connorl309/Z80-Drop-In/z80_rtl/z80_rtl.srcs/sources_1/new/data_bus_gater.v

`timescale 1ns / 1ps
//////////////////////////////////////////////////////////////////////////////////
// Company: 
// Engineer: 
// 
// Create Date: 02/15/2025 08:56:08 PM
// Design Name: 
// Module Name: data_bus_gater
// Project Name: 
// Target Devices: 
// Tool Versions: 
// Description: 
// 
// Dependencies: 
// 
// Revision:
// Revision 0.01 - File Created
// Additional Comments:
// 
//////////////////////////////////////////////////////////////////////////////////


module data_bus_gater(
    output [7:0] D_OUT,
    input [7:0] MDRL,
    input GATE_MDRL,
    input [7:0] MDRH,
    input GATE_MDRH
    );
endmodule
