connorl309/Z80-Drop-In/z80_rtl/z80_rtl.srcs/sources_1/bd/bd_tb_uart/ip/bd_tb_uart_fifo_generator_0_0/bd_tb_uart_fifo_generator_0_0_sim_netlist.v

// Copyright 1986-2022 Xilinx, Inc. All Rights Reserved.
// Copyright 2022-2024 Advanced Micro Devices, Inc. All Rights Reserved.
// --------------------------------------------------------------------------------
// Tool Version: Vivado v.2024.1 (win64) Build 5076996 Wed May 22 18:37:14 MDT 2024
// Date        : Sat Jan 25 12:34:48 2025
// Host        : UwU running 64-bit major release  (build 9200)
// Command     : write_verilog -force -mode funcsim -rename_top bd_tb_uart_fifo_generator_0_0 -prefix
//               bd_tb_uart_fifo_generator_0_0_ USB_Serial_Test_fifo_generator_1_0_sim_netlist.v
// Design      : USB_Serial_Test_fifo_generator_1_0
// Purpose     : This verilog netlist is a functional simulation representation of the design and should not be modified
//               or synthesized. This netlist cannot be used for SDF annotated simulation.
// Device      : xc7s50csga324-1
// --------------------------------------------------------------------------------
`timescale 1 ps / 1 ps

(* CHECK_LICENSE_TYPE = "USB_Serial_Test_fifo_generator_1_0,fifo_generator_v13_2_10,{}" *) (* downgradeipidentifiedwarnings = "yes" *) (* x_core_info = "fifo_generator_v13_2_10,Vivado 2024.1" *) 
(* NotValidForBitStream *)
module bd_tb_uart_fifo_generator_0_0
   (clk,
    rst,
    din,
    wr_en,
    rd_en,
    dout,
    full,
    empty);
  (* x_interface_info = "xilinx.com:signal:clock:1.0 core_clk CLK" *) (* x_interface_parameter = "XIL_INTERFACENAME core_clk, FREQ_HZ 100000000, FREQ_TOLERANCE_HZ 0, PHASE 0.0, CLK_DOMAIN /clk_wiz_0_clk_out1, INSERT_VIP 0" *) input clk;
  input rst;
  (* x_interface_info = "xilinx.com:interface:fifo_write:1.0 FIFO_WRITE WR_DATA" *) input [7:0]din;
  (* x_interface_info = "xilinx.com:interface:fifo_write:1.0 FIFO_WRITE WR_EN" *) input wr_en;
  (* x_interface_info = "xilinx.com:interface:fifo_read:1.0 FIFO_READ RD_EN" *) input rd_en;
  (* x_interface_info = "xilinx.com:interface:fifo_read:1.0 FIFO_READ RD_DATA" *) output [7:0]dout;
  (* x_interface_info = "xilinx.com:interface:fifo_write:1.0 FIFO_WRITE FULL" *) output full;
  (* x_interface_info = "xilinx.com:interface:fifo_read:1.0 FIFO_READ EMPTY" *) output empty;

  wire clk;
  wire [7:0]din;
  wire [7:0]dout;
  wire empty;
  wire full;
  wire rd_en;
  wire rst;
  wire wr_en;
  wire NLW_U0_almost_empty_UNCONNECTED;
  wire NLW_U0_almost_full_UNCONNECTED;
  wire NLW_U0_axi_ar_dbiterr_UNCONNECTED;
  wire NLW_U0_axi_ar_overflow_UNCONNECTED;
  wire NLW_U0_axi_ar_prog_empty_UNCONNECTED;
  wire NLW_U0_axi_ar_prog_full_UNCONNECTED;
  wire NLW_U0_axi_ar_sbiterr_UNCONNECTED;
  wire NLW_U0_axi_ar_underflow_UNCONNECTED;
  wire NLW_U0_axi_aw_dbiterr_UNCONNECTED;
  wire NLW_U0_axi_aw_overflow_UNCONNECTED;
  wire NLW_U0_axi_aw_prog_empty_UNCONNECTED;
  wire NLW_U0_axi_aw_prog_full_UNCONNECTED;
  wire NLW_U0_axi_aw_sbiterr_UNCONNECTED;
  wire NLW_U0_axi_aw_underflow_UNCONNECTED;
  wire NLW_U0_axi_b_dbiterr_UNCONNECTED;
  wire NLW_U0_axi_b_overflow_UNCONNECTED;
  wire NLW_U0_axi_b_prog_empty_UNCONNECTED;
  wire NLW_U0_axi_b_prog_full_UNCONNECTED;
  wire NLW_U0_axi_b_sbiterr_UNCONNECTED;
  wire NLW_U0_axi_b_underflow_UNCONNECTED;
  wire NLW_U0_axi_r_dbiterr_UNCONNECTED;
  wire NLW_U0_axi_r_overflow_UNCONNECTED;
  wire NLW_U0_axi_r_prog_empty_UNCONNECTED;
  wire NLW_U0_axi_r_prog_full_UNCONNECTED;
  wire NLW_U0_axi_r_sbiterr_UNCONNECTED;
  wire NLW_U0_axi_r_underflow_UNCONNECTED;
  wire NLW_U0_axi_w_dbiterr_UNCONNECTED;
  wire NLW_U0_axi_w_overflow_UNCONNECTED;
  wire NLW_U0_axi_w_prog_empty_UNCONNECTED;
  wire NLW_U0_axi_w_prog_full_UNCONNECTED;
  wire NLW_U0_axi_w_sbiterr_UNCONNECTED;
  wire NLW_U0_axi_w_underflow_UNCONNECTED;
  wire NLW_U0_axis_dbiterr_UNCONNECTED;
  wire NLW_U0_axis_overflow_UNCONNECTED;
  wire NLW_U0_axis_prog_empty_UNCONNECTED;
  wire NLW_U0_axis_prog_full_UNCONNECTED;
  wire NLW_U0_axis_sbiterr_UNCONNECTED;
  wire NLW_U0_axis_underflow_UNCONNECTED;
  wire NLW_U0_dbiterr_UNCONNECTED;
  wire NLW_U0_m_axi_arvalid_UNCONNECTED;
  wire NLW_U0_m_axi_awvalid_UNCONNECTED;
  wire NLW_U0_m_axi_bready_UNCONNECTED;
  wire NLW_U0_m_axi_rready_UNCONNECTED;
  wire NLW_U0_m_axi_wlast_UNCONNECTED;
  wire NLW_U0_m_axi_wvalid_UNCONNECTED;
  wire NLW_U0_m_axis_tlast_UNCONNECTED;
  wire NLW_U0_m_axis_tvalid_UNCONNECTED;
  wire NLW_U0_overflow_UNCONNECTED;
  wire NLW_U0_prog_empty_UNCONNECTED;
  wire NLW_U0_prog_full_UNCONNECTED;
  wire NLW_U0_rd_rst_busy_UNCONNECTED;
  wire NLW_U0_s_axi_arready_UNCONNECTED;
  wire NLW_U0_s_axi_awready_UNCONNECTED;
  wire NLW_U0_s_axi_bvalid_UNCONNECTED;
  wire NLW_U0_s_axi_rlast_UNCONNECTED;
  wire NLW_U0_s_axi_rvalid_UNCONNECTED;
  wire NLW_U0_s_axi_wready_UNCONNECTED;
  wire NLW_U0_s_axis_tready_UNCONNECTED;
  wire NLW_U0_sbiterr_UNCONNECTED;
  wire NLW_U0_underflow_UNCONNECTED;
  wire NLW_U0_valid_UNCONNECTED;
  wire NLW_U0_wr_ack_UNCONNECTED;
  wire NLW_U0_wr_rst_busy_UNCONNECTED;
  wire [4:0]NLW_U0_axi_ar_data_count_UNCONNECTED;
  wire [4:0]NLW_U0_axi_ar_rd_data_count_UNCONNECTED;
  wire [4:0]NLW_U0_axi_ar_wr_data_count_UNCONNECTED;
  wire [4:0]NLW_U0_axi_aw_data_count_UNCONNECTED;
  wire [4:0]NLW_U0_axi_aw_rd_data_count_UNCONNECTED;
  wire [4:0]NLW_U0_axi_aw_wr_data_count_UNCONNECTED;
  wire [4:0]NLW_U0_axi_b_data_count_UNCONNECTED;
  wire [4:0]NLW_U0_axi_b_rd_data_count_UNCONNECTED;
  wire [4:0]NLW_U0_axi_b_wr_data_count_UNCONNECTED;
  wire [10:0]NLW_U0_axi_r_data_count_UNCONNECTED;
  wire [10:0]NLW_U0_axi_r_rd_data_count_UNCONNECTED;
  wire [10:0]NLW_U0_axi_r_wr_data_count_UNCONNECTED;
  wire [10:0]NLW_U0_axi_w_data_count_UNCONNECTED;
  wire [10:0]NLW_U0_axi_w_rd_data_count_UNCONNECTED;
  wire [10:0]NLW_U0_axi_w_wr_data_count_UNCONNECTED;
  wire [10:0]NLW_U0_axis_data_count_UNCONNECTED;
  wire [10:0]NLW_U0_axis_rd_data_count_UNCONNECTED;
  wire [10:0]NLW_U0_axis_wr_data_count_UNCONNECTED;
  wire [9:0]NLW_U0_data_count_UNCONNECTED;
  wire [31:0]NLW_U0_m_axi_araddr_UNCONNECTED;
  wire [1:0]NLW_U0_m_axi_arburst_UNCONNECTED;
  wire [3:0]NLW_U0_m_axi_arcache_UNCONNECTED;
  wire [0:0]NLW_U0_m_axi_arid_UNCONNECTED;
  wire [7:0]NLW_U0_m_axi_arlen_UNCONNECTED;
  wire [0:0]NLW_U0_m_axi_arlock_UNCONNECTED;
  wire [2:0]NLW_U0_m_axi_arprot_UNCONNECTED;
  wire [3:0]NLW_U0_m_axi_arqos_UNCONNECTED;
  wire [3:0]NLW_U0_m_axi_arregion_UNCONNECTED;
  wire [2:0]NLW_U0_m_axi_arsize_UNCONNECTED;
  wire [0:0]NLW_U0_m_axi_aruser_UNCONNECTED;
  wire [31:0]NLW_U0_m_axi_awaddr_UNCONNECTED;
  wire [1:0]NLW_U0_m_axi_awburst_UNCONNECTED;
  wire [3:0]NLW_U0_m_axi_awcache_UNCONNECTED;
  wire [0:0]NLW_U0_m_axi_awid_UNCONNECTED;
  wire [7:0]NLW_U0_m_axi_awlen_UNCONNECTED;
  wire [0:0]NLW_U0_m_axi_awlock_UNCONNECTED;
  wire [2:0]NLW_U0_m_axi_awprot_UNCONNECTED;
  wire [3:0]NLW_U0_m_axi_awqos_UNCONNECTED;
  wire [3:0]NLW_U0_m_axi_awregion_UNCONNECTED;
  wire [2:0]NLW_U0_m_axi_awsize_UNCONNECTED;
  wire [0:0]NLW_U0_m_axi_awuser_UNCONNECTED;
  wire [63:0]NLW_U0_m_axi_wdata_UNCONNECTED;
  wire [0:0]NLW_U0_m_axi_wid_UNCONNECTED;
  wire [7:0]NLW_U0_m_axi_wstrb_UNCONNECTED;
  wire [0:0]NLW_U0_m_axi_wuser_UNCONNECTED;
  wire [7:0]NLW_U0_m_axis_tdata_UNCONNECTED;
  wire [0:0]NLW_U0_m_axis_tdest_UNCONNECTED;
  wire [0:0]NLW_U0_m_axis_tid_UNCONNECTED;
  wire [0:0]NLW_U0_m_axis_tkeep_UNCONNECTED;
  wire [0:0]NLW_U0_m_axis_tstrb_UNCONNECTED;
  wire [3:0]NLW_U0_m_axis_tuser_UNCONNECTED;
  wire [9:0]NLW_U0_rd_data_count_UNCONNECTED;
  wire [0:0]NLW_U0_s_axi_bid_UNCONNECTED;
  wire [1:0]NLW_U0_s_axi_bresp_UNCONNECTED;
  wire [0:0]NLW_U0_s_axi_buser_UNCONNECTED;
  wire [63:0]NLW_U0_s_axi_rdata_UNCONNECTED;
  wire [0:0]NLW_U0_s_axi_rid_UNCONNECTED;
  wire [1:0]NLW_U0_s_axi_rresp_UNCONNECTED;
  wire [0:0]NLW_U0_s_axi_ruser_UNCONNECTED;
  wire [9:0]NLW_U0_wr_data_count_UNCONNECTED;

  (* C_ADD_NGC_CONSTRAINT = "0" *) 
  (* C_APPLICATION_TYPE_AXIS = "0" *) 
  (* C_APPLICATION_TYPE_RACH = "0" *) 
  (* C_APPLICATION_TYPE_RDCH = "0" *) 
  (* C_APPLICATION_TYPE_WACH = "0" *) 
  (* C_APPLICATION_TYPE_WDCH = "0" *) 
  (* C_APPLICATION_TYPE_WRCH = "0" *) 
  (* C_AXIS_TDATA_WIDTH = "8" *) 
  (* C_AXIS_TDEST_WIDTH = "1" *) 
  (* C_AXIS_TID_WIDTH = "1" *) 
  (* C_AXIS_TKEEP_WIDTH = "1" *) 
  (* C_AXIS_TSTRB_WIDTH = "1" *) 
  (* C_AXIS_TUSER_WIDTH = "4" *) 
  (* C_AXIS_TYPE = "0" *) 
  (* C_AXI_ADDR_WIDTH = "32" *) 
  (* C_AXI_ARUSER_WIDTH = "1" *) 
  (* C_AXI_AWUSER_WIDTH = "1" *) 
  (* C_AXI_BUSER_WIDTH = "1" *) 
  (* C_AXI_DATA_WIDTH = "64" *) 
  (* C_AXI_ID_WIDTH = "1" *) 
  (* C_AXI_LEN_WIDTH = "8" *) 
  (* C_AXI_LOCK_WIDTH = "1" *) 
  (* C_AXI_RUSER_WIDTH = "1" *) 
  (* C_AXI_TYPE = "1" *) 
  (* C_AXI_WUSER_WIDTH = "1" *) 
  (* C_COMMON_CLOCK = "1" *) 
  (* C_COUNT_TYPE = "0" *) 
  (* C_DATA_COUNT_WIDTH = "10" *) 
  (* C_DEFAULT_VALUE = "BlankString" *) 
  (* C_DIN_WIDTH = "8" *) 
  (* C_DIN_WIDTH_AXIS = "1" *) 
  (* C_DIN_WIDTH_RACH = "32" *) 
  (* C_DIN_WIDTH_RDCH = "64" *) 
  (* C_DIN_WIDTH_WACH = "1" *) 
  (* C_DIN_WIDTH_WDCH = "64" *) 
  (* C_DIN_WIDTH_WRCH = "2" *) 
  (* C_DOUT_RST_VAL = "0" *) 
  (* C_DOUT_WIDTH = "8" *) 
  (* C_ENABLE_RLOCS = "0" *) 
  (* C_ENABLE_RST_SYNC = "1" *) 
  (* C_EN_SAFETY_CKT = "0" *) 
  (* C_ERROR_INJECTION_TYPE = "0" *) 
  (* C_ERROR_INJECTION_TYPE_AXIS = "0" *) 
  (* C_ERROR_INJECTION_TYPE_RACH = "0" *) 
  (* C_ERROR_INJECTION_TYPE_RDCH = "0" *) 
  (* C_ERROR_INJECTION_TYPE_WACH = "0" *) 
  (* C_ERROR_INJECTION_TYPE_WDCH = "0" *) 
  (* C_ERROR_INJECTION_TYPE_WRCH = "0" *) 
  (* C_FAMILY = "spartan7" *) 
  (* C_FULL_FLAGS_RST_VAL = "0" *) 
  (* C_HAS_ALMOST_EMPTY = "0" *) 
  (* C_HAS_ALMOST_FULL = "0" *) 
  (* C_HAS_AXIS_TDATA = "1" *) 
  (* C_HAS_AXIS_TDEST = "0" *) 
  (* C_HAS_AXIS_TID = "0" *) 
  (* C_HAS_AXIS_TKEEP = "0" *) 
  (* C_HAS_AXIS_TLAST = "0" *) 
  (* C_HAS_AXIS_TREADY = "1" *) 
  (* C_HAS_AXIS_TSTRB = "0" *) 
  (* C_HAS_AXIS_TUSER = "1" *) 
  (* C_HAS_AXI_ARUSER = "0" *) 
  (* C_HAS_AXI_AWUSER = "0" *) 
  (* C_HAS_AXI_BUSER = "0" *) 
  (* C_HAS_AXI_ID = "0" *) 
  (* C_HAS_AXI_RD_CHANNEL = "1" *) 
  (* C_HAS_AXI_RUSER = "0" *) 
  (* C_HAS_AXI_WR_CHANNEL = "1" *) 
  (* C_HAS_AXI_WUSER = "0" *) 
  (* C_HAS_BACKUP = "0" *) 
  (* C_HAS_DATA_COUNT = "0" *) 
  (* C_HAS_DATA_COUNTS_AXIS = "0" *) 
  (* C_HAS_DATA_COUNTS_RACH = "0" *) 
  (* C_HAS_DATA_COUNTS_RDCH = "0" *) 
  (* C_HAS_DATA_COUNTS_WACH = "0" *) 
  (* C_HAS_DATA_COUNTS_WDCH = "0" *) 
  (* C_HAS_DATA_COUNTS_WRCH = "0" *) 
  (* C_HAS_INT_CLK = "0" *) 
  (* C_HAS_MASTER_CE = "0" *) 
  (* C_HAS_MEMINIT_FILE = "0" *) 
  (* C_HAS_OVERFLOW = "0" *) 
  (* C_HAS_PROG_FLAGS_AXIS = "0" *) 
  (* C_HAS_PROG_FLAGS_RACH = "0" *) 
  (* C_HAS_PROG_FLAGS_RDCH = "0" *) 
  (* C_HAS_PROG_FLAGS_WACH = "0" *) 
  (* C_HAS_PROG_FLAGS_WDCH = "0" *) 
  (* C_HAS_PROG_FLAGS_WRCH = "0" *) 
  (* C_HAS_RD_DATA_COUNT = "0" *) 
  (* C_HAS_RD_RST = "0" *) 
  (* C_HAS_RST = "1" *) 
  (* C_HAS_SLAVE_CE = "0" *) 
  (* C_HAS_SRST = "0" *) 
  (* C_HAS_UNDERFLOW = "0" *) 
  (* C_HAS_VALID = "0" *) 
  (* C_HAS_WR_ACK = "0" *) 
  (* C_HAS_WR_DATA_COUNT = "0" *) 
  (* C_HAS_WR_RST = "0" *) 
  (* C_IMPLEMENTATION_TYPE = "6" *) 
  (* C_IMPLEMENTATION_TYPE_AXIS = "1" *) 
  (* C_IMPLEMENTATION_TYPE_RACH = "1" *) 
  (* C_IMPLEMENTATION_TYPE_RDCH = "1" *) 
  (* C_IMPLEMENTATION_TYPE_WACH = "1" *) 
  (* C_IMPLEMENTATION_TYPE_WDCH = "1" *) 
  (* C_IMPLEMENTATION_TYPE_WRCH = "1" *) 
  (* C_INIT_WR_PNTR_VAL = "0" *) 
  (* C_INTERFACE_TYPE = "0" *) 
  (* C_MEMORY_TYPE = "4" *) 
  (* C_MIF_FILE_NAME = "BlankString" *) 
  (* C_MSGON_VAL = "1" *) 
  (* C_OPTIMIZATION_MODE = "0" *) 
  (* C_OVERFLOW_LOW = "0" *) 
  (* C_POWER_SAVING_MODE = "0" *) 
  (* C_PRELOAD_LATENCY = "1" *) 
  (* C_PRELOAD_REGS = "0" *) 
  (* C_PRIM_FIFO_TYPE = "1kx18" *) 
  (* C_PRIM_FIFO_TYPE_AXIS = "1kx18" *) 
  (* C_PRIM_FIFO_TYPE_RACH = "512x36" *) 
  (* C_PRIM_FIFO_TYPE_RDCH = "1kx36" *) 
  (* C_PRIM_FIFO_TYPE_WACH = "512x36" *) 
  (* C_PRIM_FIFO_TYPE_WDCH = "1kx36" *) 
  (* C_PRIM_FIFO_TYPE_WRCH = "512x36" *) 
  (* C_PROG_EMPTY_THRESH_ASSERT_VAL = "2" *) 
  (* C_PROG_EMPTY_THRESH_ASSERT_VAL_AXIS = "1022" *) 
  (* C_PROG_EMPTY_THRESH_ASSERT_VAL_RACH = "1022" *) 
  (* C_PROG_EMPTY_THRESH_ASSERT_VAL_RDCH = "1022" *) 
  (* C_PROG_EMPTY_THRESH_ASSERT_VAL_WACH = "1022" *) 
  (* C_PROG_EMPTY_THRESH_ASSERT_VAL_WDCH = "1022" *) 
  (* C_PROG_EMPTY_THRESH_ASSERT_VAL_WRCH = "1022" *) 
  (* C_PROG_EMPTY_THRESH_NEGATE_VAL = "3" *) 
  (* C_PROG_EMPTY_TYPE = "0" *) 
  (* C_PROG_EMPTY_TYPE_AXIS = "0" *) 
  (* C_PROG_EMPTY_TYPE_RACH = "0" *) 
  (* C_PROG_EMPTY_TYPE_RDCH = "0" *) 
  (* C_PROG_EMPTY_TYPE_WACH = "0" *) 
  (* C_PROG_EMPTY_TYPE_WDCH = "0" *) 
  (* C_PROG_EMPTY_TYPE_WRCH = "0" *) 
  (* C_PROG_FULL_THRESH_ASSERT_VAL = "1022" *) 
  (* C_PROG_FULL_THRESH_ASSERT_VAL_AXIS = "1023" *) 
  (* C_PROG_FULL_THRESH_ASSERT_VAL_RACH = "1023" *) 
  (* C_PROG_FULL_THRESH_ASSERT_VAL_RDCH = "1023" *) 
  (* C_PROG_FULL_THRESH_ASSERT_VAL_WACH = "1023" *) 
  (* C_PROG_FULL_THRESH_ASSERT_VAL_WDCH = "1023" *) 
  (* C_PROG_FULL_THRESH_ASSERT_VAL_WRCH = "1023" *) 
  (* C_PROG_FULL_THRESH_NEGATE_VAL = "1021" *) 
  (* C_PROG_FULL_TYPE = "0" *) 
  (* C_PROG_FULL_TYPE_AXIS = "0" *) 
  (* C_PROG_FULL_TYPE_RACH = "0" *) 
  (* C_PROG_FULL_TYPE_RDCH = "0" *) 
  (* C_PROG_FULL_TYPE_WACH = "0" *) 
  (* C_PROG_FULL_TYPE_WDCH = "0" *) 
  (* C_PROG_FULL_TYPE_WRCH = "0" *) 
  (* C_RACH_TYPE = "0" *) 
  (* C_RDCH_TYPE = "0" *) 
  (* C_RD_DATA_COUNT_WIDTH = "10" *) 
  (* C_RD_DEPTH = "1024" *) 
  (* C_RD_FREQ = "1" *) 
  (* C_RD_PNTR_WIDTH = "10" *) 
  (* C_REG_SLICE_MODE_AXIS = "0" *) 
  (* C_REG_SLICE_MODE_RACH = "0" *) 
  (* C_REG_SLICE_MODE_RDCH = "0" *) 
  (* C_REG_SLICE_MODE_WACH = "0" *) 
  (* C_REG_SLICE_MODE_WDCH = "0" *) 
  (* C_REG_SLICE_MODE_WRCH = "0" *) 
  (* C_SELECT_XPM = "0" *) 
  (* C_SYNCHRONIZER_STAGE = "2" *) 
  (* C_UNDERFLOW_LOW = "0" *) 
  (* C_USE_COMMON_OVERFLOW = "0" *) 
  (* C_USE_COMMON_UNDERFLOW = "0" *) 
  (* C_USE_DEFAULT_SETTINGS = "0" *) 
  (* C_USE_DOUT_RST = "0" *) 
  (* C_USE_ECC = "0" *) 
  (* C_USE_ECC_AXIS = "0" *) 
  (* C_USE_ECC_RACH = "0" *) 
  (* C_USE_ECC_RDCH = "0" *) 
  (* C_USE_ECC_WACH = "0" *) 
  (* C_USE_ECC_WDCH = "0" *) 
  (* C_USE_ECC_WRCH = "0" *) 
  (* C_USE_EMBEDDED_REG = "0" *) 
  (* C_USE_FIFO16_FLAGS = "0" *) 
  (* C_USE_FWFT_DATA_COUNT = "0" *) 
  (* C_USE_PIPELINE_REG = "0" *) 
  (* C_VALID_LOW = "0" *) 
  (* C_WACH_TYPE = "0" *) 
  (* C_WDCH_TYPE = "0" *) 
  (* C_WRCH_TYPE = "0" *) 
  (* C_WR_ACK_LOW = "0" *) 
  (* C_WR_DATA_COUNT_WIDTH = "10" *) 
  (* C_WR_DEPTH = "1024" *) 
  (* C_WR_DEPTH_AXIS = "1024" *) 
  (* C_WR_DEPTH_RACH = "16" *) 
  (* C_WR_DEPTH_RDCH = "1024" *) 
  (* C_WR_DEPTH_WACH = "16" *) 
  (* C_WR_DEPTH_WDCH = "1024" *) 
  (* C_WR_DEPTH_WRCH = "16" *) 
  (* C_WR_FREQ = "1" *) 
  (* C_WR_PNTR_WIDTH = "10" *) 
  (* C_WR_PNTR_WIDTH_AXIS = "10" *) 
  (* C_WR_PNTR_WIDTH_RACH = "4" *) 
  (* C_WR_PNTR_WIDTH_RDCH = "10" *) 
  (* C_WR_PNTR_WIDTH_WACH = "4" *) 
  (* C_WR_PNTR_WIDTH_WDCH = "10" *) 
  (* C_WR_PNTR_WIDTH_WRCH = "4" *) 
  (* C_WR_RESPONSE_LATENCY = "1" *) 
  (* is_du_within_envelope = "true" *) 
  bd_tb_uart_fifo_generator_0_0_fifo_generator_v13_2_10 U0
       (.almost_empty(NLW_U0_almost_empty_UNCONNECTED),
        .almost_full(NLW_U0_almost_full_UNCONNECTED),
        .axi_ar_data_count(NLW_U0_axi_ar_data_count_UNCONNECTED[4:0]),
        .axi_ar_dbiterr(NLW_U0_axi_ar_dbiterr_UNCONNECTED),
        .axi_ar_injectdbiterr(1'b0),
        .axi_ar_injectsbiterr(1'b0),
        .axi_ar_overflow(NLW_U0_axi_ar_overflow_UNCONNECTED),
        .axi_ar_prog_empty(NLW_U0_axi_ar_prog_empty_UNCONNECTED),
        .axi_ar_prog_empty_thresh({1'b0,1'b0,1'b0,1'b0}),
        .axi_ar_prog_full(NLW_U0_axi_ar_prog_full_UNCONNECTED),
        .axi_ar_prog_full_thresh({1'b0,1'b0,1'b0,1'b0}),
        .axi_ar_rd_data_count(NLW_U0_axi_ar_rd_data_count_UNCONNECTED[4:0]),
        .axi_ar_sbiterr(NLW_U0_axi_ar_sbiterr_UNCONNECTED),
        .axi_ar_underflow(NLW_U0_axi_ar_underflow_UNCONNECTED),
        .axi_ar_wr_data_count(NLW_U0_axi_ar_wr_data_count_UNCONNECTED[4:0]),
        .axi_aw_data_count(NLW_U0_axi_aw_data_count_UNCONNECTED[4:0]),
        .axi_aw_dbiterr(NLW_U0_axi_aw_dbiterr_UNCONNECTED),
        .axi_aw_injectdbiterr(1'b0),
        .axi_aw_injectsbiterr(1'b0),
        .axi_aw_overflow(NLW_U0_axi_aw_overflow_UNCONNECTED),
        .axi_aw_prog_empty(NLW_U0_axi_aw_prog_empty_UNCONNECTED),
        .axi_aw_prog_empty_thresh({1'b0,1'b0,1'b0,1'b0}),
        .axi_aw_prog_full(NLW_U0_axi_aw_prog_full_UNCONNECTED),
        .axi_aw_prog_full_thresh({1'b0,1'b0,1'b0,1'b0}),
        .axi_aw_rd_data_count(NLW_U0_axi_aw_rd_data_count_UNCONNECTED[4:0]),
        .axi_aw_sbiterr(NLW_U0_axi_aw_sbiterr_UNCONNECTED),
        .axi_aw_underflow(NLW_U0_axi_aw_underflow_UNCONNECTED),
        .axi_aw_wr_data_count(NLW_U0_axi_aw_wr_data_count_UNCONNECTED[4:0]),
        .axi_b_data_count(NLW_U0_axi_b_data_count_UNCONNECTED[4:0]),
        .axi_b_dbiterr(NLW_U0_axi_b_dbiterr_UNCONNECTED),
        .axi_b_injectdbiterr(1'b0),
        .axi_b_injectsbiterr(1'b0),
        .axi_b_overflow(NLW_U0_axi_b_overflow_UNCONNECTED),
        .axi_b_prog_empty(NLW_U0_axi_b_prog_empty_UNCONNECTED),
        .axi_b_prog_empty_thresh({1'b0,1'b0,1'b0,1'b0}),
        .axi_b_prog_full(NLW_U0_axi_b_prog_full_UNCONNECTED),
        .axi_b_prog_full_thresh({1'b0,1'b0,1'b0,1'b0}),
        .axi_b_rd_data_count(NLW_U0_axi_b_rd_data_count_UNCONNECTED[4:0]),
        .axi_b_sbiterr(NLW_U0_axi_b_sbiterr_UNCONNECTED),
        .axi_b_underflow(NLW_U0_axi_b_underflow_UNCONNECTED),
        .axi_b_wr_data_count(NLW_U0_axi_b_wr_data_count_UNCONNECTED[4:0]),
        .axi_r_data_count(NLW_U0_axi_r_data_count_UNCONNECTED[10:0]),
        .axi_r_dbiterr(NLW_U0_axi_r_dbiterr_UNCONNECTED),
        .axi_r_injectdbiterr(1'b0),
        .axi_r_injectsbiterr(1'b0),
        .axi_r_overflow(NLW_U0_axi_r_overflow_UNCONNECTED),
        .axi_r_prog_empty(NLW_U0_axi_r_prog_empty_UNCONNECTED),
        .axi_r_prog_empty_thresh({1'b0,1'b0,1'b0,1'b0,1'b0,1'b0,1'b0,1'b0,1'b0,1'b0}),
        .axi_r_prog_full(NLW_U0_axi_r_prog_full_UNCONNECTED),
        .axi_r_prog_full_thresh({1'b0,1'b0,1'b0,1'b0,1'b0,1'b0,1'b0,1'b0,1'b0,1'b0}),
        .axi_r_rd_data_count(NLW_U0_axi_r_rd_data_count_UNCONNECTED[10:0]),
        .axi_r_sbiterr(NLW_U0_axi_r_sbiterr_UNCONNECTED),
        .axi_r_underflow(NLW_U0_axi_r_underflow_UNCONNECTED),
        .axi_r_wr_data_count(NLW_U0_axi_r_wr_data_count_UNCONNECTED[10:0]),
        .axi_w_data_count(NLW_U0_axi_w_data_count_UNCONNECTED[10:0]),
        .axi_w_dbiterr(NLW_U0_axi_w_dbiterr_UNCONNECTED),
        .axi_w_injectdbiterr(1'b0),
        .axi_w_injectsbiterr(1'b0),
        .axi_w_overflow(NLW_U0_axi_w_overflow_UNCONNECTED),
        .axi_w_prog_empty(NLW_U0_axi_w_prog_empty_UNCONNECTED),
        .axi_w_prog_empty_thresh({1'b0,1'b0,1'b0,1'b0,1'b0,1'b0,1'b0,1'b0,1'b0,1'b0}),
        .axi_w_prog_full(NLW_U0_axi_w_prog_full_UNCONNECTED),
        .axi_w_prog_full_thresh({1'b0,1'b0,1'b0,1'b0,1'b0,1'b0,1'b0,1'b0,1'b0,1'b0}),
        .axi_w_rd_data_count(NLW_U0_axi_w_rd_data_count_UNCONNECTED[10:0]),
        .axi_w_sbiterr(NLW_U0_axi_w_sbiterr_UNCONNECTED),
        .axi_w_underflow(NLW_U0_axi_w_underflow_UNCONNECTED),
        .axi_w_wr_data_count(NLW_U0_axi_w_wr_data_count_UNCONNECTED[10:0]),
        .axis_data_count(NLW_U0_axis_data_count_UNCONNECTED[10:0]),
        .axis_dbiterr(NLW_U0_axis_dbiterr_UNCONNECTED),
        .axis_injectdbiterr(1'b0),
        .axis_injectsbiterr(1'b0),
        .axis_overflow(NLW_U0_axis_overflow_UNCONNECTED),
        .axis_prog_empty(NLW_U0_axis_prog_empty_UNCONNECTED),
        .axis_prog_empty_thresh({1'b0,1'b0,1'b0,1'b0,1'b0,1'b0,1'b0,1'b0,1'b0,1'b0}),
        .axis_prog_full(NLW_U0_axis_prog_full_UNCONNECTED),
        .axis_prog_full_thresh({1'b0,1'b0,1'b0,1'b0,1'b0,1'b0,1'b0,1'b0,1'b0,1'b0}),
        .axis_rd_data_count(NLW_U0_axis_rd_data_count_UNCONNECTED[10:0]),
        .axis_sbiterr(NLW_U0_axis_sbiterr_UNCONNECTED),
        .axis_underflow(NLW_U0_axis_underflow_UNCONNECTED),
        .axis_wr_data_count(NLW_U0_axis_wr_data_count_UNCONNECTED[10:0]),
        .backup(1'b0),
        .backup_marker(1'b0),
        .clk(clk),
        .data_count(NLW_U0_data_count_UNCONNECTED[9:0]),
        .dbiterr(NLW_U0_dbiterr_UNCONNECTED),
        .din(din),
        .dout(dout),
        .empty(empty),
        .full(full),
        .injectdbiterr(1'b0),
        .injectsbiterr(1'b0),
        .int_clk(1'b0),
        .m_aclk(1'b0),
        .m_aclk_en(1'b0),
        .m_axi_araddr(NLW_U0_m_axi_araddr_UNCONNECTED[31:0]),
        .m_axi_arburst(NLW_U0_m_axi_arburst_UNCONNECTED[1:0]),
        .m_axi_arcache(NLW_U0_m_axi_arcache_UNCONNECTED[3:0]),
        .m_axi_arid(NLW_U0_m_axi_arid_UNCONNECTED[0]),
        .m_axi_arlen(NLW_U0_m_axi_arlen_UNCONNECTED[7:0]),
        .m_axi_arlock(NLW_U0_m_axi_arlock_UNCONNECTED[0]),
        .m_axi_arprot(NLW_U0_m_axi_arprot_UNCONNECTED[2:0]),
        .m_axi_arqos(NLW_U0_m_axi_arqos_UNCONNECTED[3:0]),
        .m_axi_arready(1'b0),
        .m_axi_arregion(NLW_U0_m_axi_arregion_UNCONNECTED[3:0]),
        .m_axi_arsize(NLW_U0_m_axi_arsize_UNCONNECTED[2:0]),
        .m_axi_aruser(NLW_U0_m_axi_aruser_UNCONNECTED[0]),
        .m_axi_arvalid(NLW_U0_m_axi_arvalid_UNCONNECTED),
        .m_axi_awaddr(NLW_U0_m_axi_awaddr_UNCONNECTED[31:0]),
        .m_axi_awburst(NLW_U0_m_axi_awburst_UNCONNECTED[1:0]),
        .m_axi_awcache(NLW_U0_m_axi_awcache_UNCONNECTED[3:0]),
        .m_axi_awid(NLW_U0_m_axi_awid_UNCONNECTED[0]),
        .m_axi_awlen(NLW_U0_m_axi_awlen_UNCONNECTED[7:0]),
        .m_axi_awlock(NLW_U0_m_axi_awlock_UNCONNECTED[0]),
        .m_axi_awprot(NLW_U0_m_axi_awprot_UNCONNECTED[2:0]),
        .m_axi_awqos(NLW_U0_m_axi_awqos_UNCONNECTED[3:0]),
        .m_axi_awready(1'b0),
        .m_axi_awregion(NLW_U0_m_axi_awregion_UNCONNECTED[3:0]),
        .m_axi_awsize(NLW_U0_m_axi_awsize_UNCONNECTED[2:0]),
        .m_axi_awuser(NLW_U0_m_axi_awuser_UNCONNECTED[0]),
        .m_axi_awvalid(NLW_U0_m_axi_awvalid_UNCONNECTED),
        .m_axi_bid(1'b0),
        .m_axi_bready(NLW_U0_m_axi_bready_UNCONNECTED),
        .m_axi_bresp({1'b0,1'b0}),
        .m_axi_buser(1'b0),
        .m_axi_bvalid(1'b0),
        .m_axi_rdata({1'b0,1'b0,1'b0,1'b0,1'b0,1'b0,1'b0,1'b0,1'b0,1'b0,1'b0,1'b0,1'b0,1'b0,1'b0,1'b0,1'b0,1'b0,1'b0,1'b0,1'b0,1'b0,1'b0,1'b0,1'b0,1'b0,1'b0,1'b0,1'b0,1'b0,1'b0,1'b0,1'b0,1'b0,1'b0,1'b0,1'b0,1'b0,1'b0,1'b0,1'b0,1'b0,1'b0,1'b0,1'b0,1'b0,1'b0,1'b0,1'b0,1'b0,1'b0,1'b0,1'b0,1'b0,1'b0,1'b0,1'b0,1'b0,1'b0,1'b0,1'b0,1'b0,1'b0,1'b0}),
        .m_axi_rid(1'b0),
        .m_axi_rlast(1'b0),
        .m_axi_rready(NLW_U0_m_axi_rready_UNCONNECTED),
        .m_axi_rresp({1'b0,1'b0}),
        .m_axi_ruser(1'b0),
        .m_axi_rvalid(1'b0),
        .m_axi_wdata(NLW_U0_m_axi_wdata_UNCONNECTED[63:0]),
        .m_axi_wid(NLW_U0_m_axi_wid_UNCONNECTED[0]),
        .m_axi_wlast(NLW_U0_m_axi_wlast_UNCONNECTED),
        .m_axi_wready(1'b0),
        .m_axi_wstrb(NLW_U0_m_axi_wstrb_UNCONNECTED[7:0]),
        .m_axi_wuser(NLW_U0_m_axi_wuser_UNCONNECTED[0]),
        .m_axi_wvalid(NLW_U0_m_axi_wvalid_UNCONNECTED),
        .m_axis_tdata(NLW_U0_m_axis_tdata_UNCONNECTED[7:0]),
        .m_axis_tdest(NLW_U0_m_axis_tdest_UNCONNECTED[0]),
        .m_axis_tid(NLW_U0_m_axis_tid_UNCONNECTED[0]),
        .m_axis_tkeep(NLW_U0_m_axis_tkeep_UNCONNECTED[0]),
        .m_axis_tlast(NLW_U0_m_axis_tlast_UNCONNECTED),
        .m_axis_tready(1'b0),
        .m_axis_tstrb(NLW_U0_m_axis_tstrb_UNCONNECTED[0]),
        .m_axis_tuser(NLW_U0_m_axis_tuser_UNCONNECTED[3:0]),
        .m_axis_tvalid(NLW_U0_m_axis_tvalid_UNCONNECTED),
        .overflow(NLW_U0_overflow_UNCONNECTED),
        .prog_empty(NLW_U0_prog_empty_UNCONNECTED),
        .prog_empty_thresh({1'b0,1'b0,1'b0,1'b0,1'b0,1'b0,1'b0,1'b0,1'b0,1'b0}),
        .prog_empty_thresh_assert({1'b0,1'b0,1'b0,1'b0,1'b0,1'b0,1'b0,1'b0,1'b0,1'b0}),
        .prog_empty_thresh_negate({1'b0,1'b0,1'b0,1'b0,1'b0,1'b0,1'b0,1'b0,1'b0,1'b0}),
        .prog_full(NLW_U0_prog_full_UNCONNECTED),
        .prog_full_thresh({1'b0,1'b0,1'b0,1'b0,1'b0,1'b0,1'b0,1'b0,1'b0,1'b0}),
        .prog_full_thresh_assert({1'b0,1'b0,1'b0,1'b0,1'b0,1'b0,1'b0,1'b0,1'b0,1'b0}),
        .prog_full_thresh_negate({1'b0,1'b0,1'b0,1'b0,1'b0,1'b0,1'b0,1'b0,1'b0,1'b0}),
        .rd_clk(1'b0),
        .rd_data_count(NLW_U0_rd_data_count_UNCONNECTED[9:0]),
        .rd_en(rd_en),
        .rd_rst(1'b0),
        .rd_rst_busy(NLW_U0_rd_rst_busy_UNCONNECTED),
        .rst(rst),
        .s_aclk(1'b0),
        .s_aclk_en(1'b0),
        .s_aresetn(1'b0),
        .s_axi_araddr({1'b0,1'b0,1'b0,1'b0,1'b0,1'b0,1'b0,1'b0,1'b0,1'b0,1'b0,1'b0,1'b0,1'b0,1'b0,1'b0,1'b0,1'b0,1'b0,1'b0,1'b0,1'b0,1'b0,1'b0,1'b0,1'b0,1'b0,1'b0,1'b0,1'b0,1'b0,1'b0}),
        .s_axi_arburst({1'b0,1'b0}),
        .s_axi_arcache({1'b0,1'b0,1'b0,1'b0}),
        .s_axi_arid(1'b0),
        .s_axi_arlen({1'b0,1'b0,1'b0,1'b0,1'b0,1'b0,1'b0,1'b0}),
        .s_axi_arlock(1'b0),
        .s_axi_arprot({1'b0,1'b0,1'b0}),
        .s_axi_arqos({1'b0,1'b0,1'b0,1'b0}),
        .s_axi_arready(NLW_U0_s_axi_arready_UNCONNECTED),
        .s_axi_arregion({1'b0,1'b0,1'b0,1'b0}),
        .s_axi_arsize({1'b0,1'b0,1'b0}),
        .s_axi_aruser(1'b0),
        .s_axi_arvalid(1'b0),
        .s_axi_awaddr({1'b0,1'b0,1'b0,1'b0,1'b0,1'b0,1'b0,1'b0,1'b0,1'b0,1'b0,1'b0,1'b0,1'b0,1'b0,1'b0,1'b0,1'b0,1'b0,1'b0,1'b0,1'b0,1'b0,1'b0,1'b0,1'b0,1'b0,1'b0,1'b0,1'b0,1'b0,1'b0}),
        .s_axi_awburst({1'b0,1'b0}),
        .s_axi_awcache({1'b0,1'b0,1'b0,1'b0}),
        .s_axi_awid(1'b0),
        .s_axi_awlen({1'b0,1'b0,1'b0,1'b0,1'b0,1'b0,1'b0,1'b0}),
        .s_axi_awlock(1'b0),
        .s_axi_awprot({1'b0,1'b0,1'b0}),
        .s_axi_awqos({1'b0,1'b0,1'b0,1'b0}),
        .s_axi_awready(NLW_U0_s_axi_awready_UNCONNECTED),
        .s_axi_awregion({1'b0,1'b0,1'b0,1'b0}),
        .s_axi_awsize({1'b0,1'b0,1'b0}),
        .s_axi_awuser(1'b0),
        .s_axi_awvalid(1'b0),
        .s_axi_bid(NLW_U0_s_axi_bid_UNCONNECTED[0]),
        .s_axi_bready(1'b0),
        .s_axi_bresp(NLW_U0_s_axi_bresp_UNCONNECTED[1:0]),
        .s_axi_buser(NLW_U0_s_axi_buser_UNCONNECTED[0]),
        .s_axi_bvalid(NLW_U0_s_axi_bvalid_UNCONNECTED),
        .s_axi_rdata(NLW_U0_s_axi_rdata_UNCONNECTED[63:0]),
        .s_axi_rid(NLW_U0_s_axi_rid_UNCONNECTED[0]),
        .s_axi_rlast(NLW_U0_s_axi_rlast_UNCONNECTED),
        .s_axi_rready(1'b0),
        .s_axi_rresp(NLW_U0_s_axi_rresp_UNCONNECTED[1:0]),
        .s_axi_ruser(NLW_U0_s_axi_ruser_UNCONNECTED[0]),
        .s_axi_rvalid(NLW_U0_s_axi_rvalid_UNCONNECTED),
        .s_axi_wdata({1'b0,1'b0,1'b0,1'b0,1'b0,1'b0,1'b0,1'b0,1'b0,1'b0,1'b0,1'b0,1'b0,1'b0,1'b0,1'b0,1'b0,1'b0,1'b0,1'b0,1'b0,1'b0,1'b0,1'b0,1'b0,1'b0,1'b0,1'b0,1'b0,1'b0,1'b0,1'b0,1'b0,1'b0,1'b0,1'b0,1'b0,1'b0,1'b0,1'b0,1'b0,1'b0,1'b0,1'b0,1'b0,1'b0,1'b0,1'b0,1'b0,1'b0,1'b0,1'b0,1'b0,1'b0,1'b0,1'b0,1'b0,1'b0,1'b0,1'b0,1'b0,1'b0,1'b0,1'b0}),
        .s_axi_wid(1'b0),
        .s_axi_wlast(1'b0),
        .s_axi_wready(NLW_U0_s_axi_wready_UNCONNECTED),
        .s_axi_wstrb({1'b0,1'b0,1'b0,1'b0,1'b0,1'b0,1'b0,1'b0}),
        .s_axi_wuser(1'b0),
        .s_axi_wvalid(1'b0),
        .s_axis_tdata({1'b0,1'b0,1'b0,1'b0,1'b0,1'b0,1'b0,1'b0}),
        .s_axis_tdest(1'b0),
        .s_axis_tid(1'b0),
        .s_axis_tkeep(1'b0),
        .s_axis_tlast(1'b0),
        .s_axis_tready(NLW_U0_s_axis_tready_UNCONNECTED),
        .s_axis_tstrb(1'b0),
        .s_axis_tuser({1'b0,1'b0,1'b0,1'b0}),
        .s_axis_tvalid(1'b0),
        .sbiterr(NLW_U0_sbiterr_UNCONNECTED),
        .sleep(1'b0),
        .srst(1'b0),
        .underflow(NLW_U0_underflow_UNCONNECTED),
        .valid(NLW_U0_valid_UNCONNECTED),
        .wr_ack(NLW_U0_wr_ack_UNCONNECTED),
        .wr_clk(1'b0),
        .wr_data_count(NLW_U0_wr_data_count_UNCONNECTED[9:0]),
        .wr_en(wr_en),
        .wr_rst(1'b0),
        .wr_rst_busy(NLW_U0_wr_rst_busy_UNCONNECTED));
endmodule
`pragma protect begin_protected
`pragma protect version = 1
`pragma protect encrypt_agent = "XILINX"
`pragma protect encrypt_agent_info = "Xilinx Encryption Tool 2024.1"
`pragma protect key_keyowner="Synopsys", key_keyname="SNPS-VCS-RSA-2", key_method="rsa"
`pragma protect encoding = (enctype="BASE64", line_length=76, bytes=128)
`pragma protect key_block
VRufLWT3xuzTvQKo8VrgeA7TQuqzWEYy/B1VZF2gTA62OnYpyvfz/jYVlv8uQmDxe/ByRttr4gwP
tNck8lOlu04WorDYZXBY99Iv+CD1MRsK+y6klNIUbRWjkWmJ0jF7xfzo5v6+6GlaIHD1nYWB0BGS
XKOLLgkxdDTc9QzwJD4=

`pragma protect key_keyowner="Aldec", key_keyname="ALDEC15_001", key_method="rsa"
`pragma protect encoding = (enctype="BASE64", line_length=76, bytes=256)
`pragma protect key_block
uL+N2Y0N0Nss4UIbL4YgwYw1dJAEJxw9VgIJekBqgLF5Hu0OvgBycKBL3tx4bMFtXLoBUh2ZjpPa
Go57AlryR20NeXp3+hoQeboPP11E649UsEN94qUxaPWE5/ujAWzWT8PMJfk3CAspcIaP3XsDNcxF
vPCbKLRNyWvSzyiofwOXgxNNgLi38SzcrWZtPo/eMELIxeVE3bkV2B7I60W9KI1gXiOj3SjPTDnx
EMAbJCwmbwCkTXljtuzvIRTsGb9QIurgASMwg4IWmb9DS6EbeVgoWu9ePD+YKuN3LcW87KSgmC3y
Mirx3ScsFGRfcOAUOLlOQxU4qqE1ZAjtBAua1w==

`pragma protect key_keyowner="Mentor Graphics Corporation", key_keyname="MGC-VELOCE-RSA", key_method="rsa"
`pragma protect encoding = (enctype="BASE64", line_length=76, bytes=128)
`pragma protect key_block
ngggZ4AaOolK7F7zeqf8LCxDCGfbvArfgDzbRvoxE+aIi2H2/ZgHbrcaf1Km1cW+38j2kTOpZ5BU
JUI2G5HZNfsoiLXjFbOMvQQqByNzlhCZjrS3N725Cznvy/nQpUy+kW4iA6DQZKnpdC2s18Suxi5p
XtgDcUzCh62ABICOpz8=

`pragma protect key_keyowner="Mentor Graphics Corporation", key_keyname="MGC-VERIF-SIM-RSA-2", key_method="rsa"
`pragma protect encoding = (enctype="BASE64", line_length=76, bytes=256)
`pragma protect key_block
FzAmLTVxyHRqX0WAddlPopAH/5r3ExgkeVujmhMcJXHbjZ+OKAHOMXTsnwDh03EpZ2Dn+0UPeR9J
JML3A+MQGMuUUzy/4d/lj5rriSnTu0eRK0uK6Gl8vjL08vO3UKb6wGj/w9CP45OWOkbMNgZzJkAl
ulPX0OUqymWYOn3WVAtIlaQ0dmpONV8p6Ixe9p5wlEtvy+7JjUPwaVnKlLjKSAaYD07OqMK+IOEP
5oYs2BscpZ3YKlKVJkoU493L7szHHn2LhSUrMld33nLuWIO6WPdo2u2pTnWXl/J1BzNaK1VaLx4R
H7VhIvgYcSlzCrtbQuNHKFtDPGhXjeA41TS29g==

`pragma protect key_keyowner="Real Intent", key_keyname="RI-RSA-KEY-1", key_method="rsa"
`pragma protect encoding = (enctype="BASE64", line_length=76, bytes=256)
`pragma protect key_block
Oad6Ezs+KRRjlYrAkExu4Kft2T1qNa0HGt8W7O1ByK1ecBs0TGWt/sS3pnt6d6jWuqvsWhrmcGsU
TD7Z+IY65xRZ4IJfgngZD8v540FOGMuFUS31UWxcC7CI6qOo20Q0Irtoxrqm01u5p3tI87ApsE8S
lc2lQ5dh54cGYlRfmo5mYTw6WSHyyVYmoh9npUliD4eNVIKUqnBo1kmYzicnKe8ewFKTEWpjdMeZ
/4YxF/NRZzHTA3GIsnjcgOHia68T/NJJ+zQmoNwxerZWWoacU1EU0IHxET3y4fS/u0Af8OJhkGQf
jI0jGobNLRYYufemCxL6333z0oAno0RiPZlavA==

`pragma protect key_keyowner="Xilinx", key_keyname="xilinxt_2023_11", key_method="rsa"
`pragma protect encoding = (enctype="BASE64", line_length=76, bytes=256)
`pragma protect key_block
LVIUY1x0cEHel3aUfppGw9v6zvpZmh/zrCgsFGWLi8t0vWUC/ikETYOpuFw/0f9L2t8c6tQj/BSQ
wjvzq42gFgtW+CFBjgHAVUBDHhzlv/GKUM/2Vq36bMg9H5f44nJH+7mDDGVPf2PyYZRkAosFPUpA
wRqTC/g2mQ0mMY/gZGQRrs+/VY69Ze9sjoEiEXuwkb/+/VjXgHCxiCzG4cKf0ZiQ+rePhqJqB7FK
IJ+6LHriZD474qtFLq3fOZ9mrqOgN7iBQlc66dO9E0RmZZZsWtQQzZ4q1c2pzvsjDdJyWe0mTlwa
QGVmYElSvL9in5WwDxoKM+2J7vco8OIexLgbJg==

`pragma protect key_keyowner="Metrics Technologies Inc.", key_keyname="DSim", key_method="rsa"
`pragma protect encoding = (enctype="BASE64", line_length=76, bytes=256)
`pragma protect key_block
Qf9CPkJTDS6nRjzJ66HoyvpTqtDB4QY3Hy9peOp3xA39ggAvytqhHhiPv35dCRWSCdAyO1u2m+O7
/knms947I+MYTpHHfukyZsBbLho0jRq3cSXe9e6VE+4Dt40wryd91cmi93qmeUxg+vf0F91ug50P
gJ4oGYP71ANEq1UaGqGHgVK0ZsY6jTyc0x25eh+fnXg6vElSbqcptvyGMOBVT/g+gDKIheN40WzZ
Tday7b7o8j+UecVazn9OG8lGmgEQH+ilZfelpEFOBKoEc7YS6kKJ1yiX5nxRMJalTuojq5mhxebk
EsmPJe45gdIAuAmBpw3iLddcx52Arew1xpNY9w==

`pragma protect key_keyowner="Atrenta", key_keyname="ATR-SG-RSA-1", key_method="rsa"
`pragma protect encoding = (enctype="BASE64", line_length=76, bytes=384)
`pragma protect key_block
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

`pragma protect key_keyowner="Cadence Design Systems.", key_keyname="CDS_RSA_KEY_VER_1", key_method="rsa"
`pragma protect encoding = (enctype="BASE64", line_length=76, bytes=256)
`pragma protect key_block
WXM4aFffz6byfeUnRWfxJR3Sbg31hpZIfhJu9O4aqVdZMRQzhrArOJ75qYkGOgZjI+35a4DA9Ohc
RMh3Tm8A5kh9XM67B45s3+7vF8pYIM5pFlzEQBSQ/OeeAi6GNLI2ACXQl1WutRpQKuwX9iboEsRb
Kc1SU6AOV6yaliF6tUt1LL4x+bC8mqlEHTk6SvN7aiA23tVDcik1QSH66CO3/+J5f88G53DHDqtY
T6w2k7pUziwTnLfirI+XpPgqYp9YYRQEv52Q7wTYJlYnVYrMyludNuTaIE27AkgPAneEkdJlrq9l
eVOgs6ZIO1DEusKG7VzkbM1sS0GnU5Zhuj1Eww==

`pragma protect key_keyowner="Synplicity", key_keyname="SYNP15_1", key_method="rsa"
`pragma protect encoding = (enctype="BASE64", line_length=76, bytes=256)
`pragma protect key_block
KJ2iLB3UgRnxezAEg3KJ/gREzXcLo8pOtacMRsDMsFCSD3vYAdGUKSARO8g71pIGFzJo6PBwogFR
MkJED/0TqwZaleoFaN2ULuSnzZGmf8vT0qKvutBGquDn8MH7T3k3wLxcNdZQLnkqisJCMj8u+71g
xMQRAkhtAQvA2cWb6TDQN6jmfByZuu/AH3X+YZ43XIDG/jymNkwyBWNNx0yzbZouJtOuzzYHhYoC
AAuKR+zfynO91P9hcrXFiExHtCmvb73DA4ICLGiOzEj+C1PMPBX9AHdhnWYy5BbQGsd727Y50yNo
xmTU1vBKL2ewwN4j/Ib2AK/Z7T+d/NunpRbCnA==

`pragma protect key_keyowner="Mentor Graphics Corporation", key_keyname="MGC-PREC-RSA", key_method="rsa"
`pragma protect encoding = (enctype="BASE64", line_length=76, bytes=256)
`pragma protect key_block
eYDP9MWXRUmO05etuHvoqbEMRNQHmR5nos71kLkRxpycXrdpHxalQmyEdCdbeVoM8lN9qwxKuN0l
yQn00dSYRi3P02ygaVsHqVAsRtz2yRpIRjyGMYD7zKpnNQw476DBmK+/sCD7EH6NxSfzUNnfoURL
uIFC0sHEYpwX6Qt2bT2GdCC0OFvaGwQNimyTFdfeey7cdpg9JmsQRgLEUfRwG1Dk0iu258zTUnT+
31O5RA9OwlgZJpC+LpCvL8XAmGZJ4CCeUf2hnpppoV4KphAV4mCBUkNtUYZSJdF0a5cdHFxnxR5n
nI0ed4USMMiNvLqvP0HQgecfCvYzYx9kk0bmtA==

`pragma protect data_method = "AES128-CBC"
`pragma protect encoding = (enctype = "BASE64", line_length = 76, bytes = 51680)
`pragma protect data_block
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
`pragma protect end_protected
`ifndef GLBL
`define GLBL
`timescale  1 ps / 1 ps

module glbl ();

    parameter ROC_WIDTH = 100000;
    parameter TOC_WIDTH = 0;
    parameter GRES_WIDTH = 10000;
    parameter GRES_START = 10000;

//--------   STARTUP Globals --------------
    wire GSR;
    wire GTS;
    wire GWE;
    wire PRLD;
    wire GRESTORE;
    tri1 p_up_tmp;
    tri (weak1, strong0) PLL_LOCKG = p_up_tmp;

    wire PROGB_GLBL;
    wire CCLKO_GLBL;
    wire FCSBO_GLBL;
    wire [3:0] DO_GLBL;
    wire [3:0] DI_GLBL;
   
    reg GSR_int;
    reg GTS_int;
    reg PRLD_int;
    reg GRESTORE_int;

//--------   JTAG Globals --------------
    wire JTAG_TDO_GLBL;
    wire JTAG_TCK_GLBL;
    wire JTAG_TDI_GLBL;
    wire JTAG_TMS_GLBL;
    wire JTAG_TRST_GLBL;

    reg JTAG_CAPTURE_GLBL;
    reg JTAG_RESET_GLBL;
    reg JTAG_SHIFT_GLBL;
    reg JTAG_UPDATE_GLBL;
    reg JTAG_RUNTEST_GLBL;

    reg JTAG_SEL1_GLBL = 0;
    reg JTAG_SEL2_GLBL = 0 ;
    reg JTAG_SEL3_GLBL = 0;
    reg JTAG_SEL4_GLBL = 0;

    reg JTAG_USER_TDO1_GLBL = 1'bz;
    reg JTAG_USER_TDO2_GLBL = 1'bz;
    reg JTAG_USER_TDO3_GLBL = 1'bz;
    reg JTAG_USER_TDO4_GLBL = 1'bz;

    assign (strong1, weak0) GSR = GSR_int;
    assign (strong1, weak0) GTS = GTS_int;
    assign (weak1, weak0) PRLD = PRLD_int;
    assign (strong1, weak0) GRESTORE = GRESTORE_int;

    initial begin
	GSR_int = 1'b1;
	PRLD_int = 1'b1;
	#(ROC_WIDTH)
	GSR_int = 1'b0;
	PRLD_int = 1'b0;
    end

    initial begin
	GTS_int = 1'b1;
	#(TOC_WIDTH)
	GTS_int = 1'b0;
    end

    initial begin 
	GRESTORE_int = 1'b0;
	#(GRES_START);
	GRESTORE_int = 1'b1;
	#(GRES_WIDTH);
	GRESTORE_int = 1'b0;
    end

endmodule
`endif
