connorl309/Z80-Drop-In/z80_rtl/z80_rtl.srcs/sources_1/bd/bd_tb_uart/ip/bd_tb_uart_fifo_generator_0_0/bd_tb_uart_fifo_generator_0_0_sim_netlist.vhdl

-- Copyright 1986-2022 Xilinx, Inc. All Rights Reserved.
-- Copyright 2022-2024 Advanced Micro Devices, Inc. All Rights Reserved.
-- --------------------------------------------------------------------------------
-- Tool Version: Vivado v.2024.1 (win64) Build 5076996 Wed May 22 18:37:14 MDT 2024
-- Date        : Sat Jan 25 12:34:48 2025
-- Host        : UwU running 64-bit major release  (build 9200)
-- Command     : write_vhdl -force -mode funcsim -rename_top bd_tb_uart_fifo_generator_0_0 -prefix
--               bd_tb_uart_fifo_generator_0_0_ USB_Serial_Test_fifo_generator_1_0_sim_netlist.vhdl
-- Design      : USB_Serial_Test_fifo_generator_1_0
-- Purpose     : This VHDL netlist is a functional simulation representation of the design and should not be modified or
--               synthesized. This netlist cannot be used for SDF annotated simulation.
-- Device      : xc7s50csga324-1
-- --------------------------------------------------------------------------------
`protect begin_protected
`protect version = 1
`protect encrypt_agent = "XILINX"
`protect encrypt_agent_info = "Xilinx Encryption Tool 2024.1"
`protect key_keyowner="Synopsys", key_keyname="SNPS-VCS-RSA-2", key_method="rsa"
`protect encoding = (enctype="BASE64", line_length=76, bytes=128)
`protect key_block
VRufLWT3xuzTvQKo8VrgeA7TQuqzWEYy/B1VZF2gTA62OnYpyvfz/jYVlv8uQmDxe/ByRttr4gwP
tNck8lOlu04WorDYZXBY99Iv+CD1MRsK+y6klNIUbRWjkWmJ0jF7xfzo5v6+6GlaIHD1nYWB0BGS
XKOLLgkxdDTc9QzwJD4=

`protect key_keyowner="Aldec", key_keyname="ALDEC15_001", key_method="rsa"
`protect encoding = (enctype="BASE64", line_length=76, bytes=256)
`protect key_block
uL+N2Y0N0Nss4UIbL4YgwYw1dJAEJxw9VgIJekBqgLF5Hu0OvgBycKBL3tx4bMFtXLoBUh2ZjpPa
Go57AlryR20NeXp3+hoQeboPP11E649UsEN94qUxaPWE5/ujAWzWT8PMJfk3CAspcIaP3XsDNcxF
vPCbKLRNyWvSzyiofwOXgxNNgLi38SzcrWZtPo/eMELIxeVE3bkV2B7I60W9KI1gXiOj3SjPTDnx
EMAbJCwmbwCkTXljtuzvIRTsGb9QIurgASMwg4IWmb9DS6EbeVgoWu9ePD+YKuN3LcW87KSgmC3y
Mirx3ScsFGRfcOAUOLlOQxU4qqE1ZAjtBAua1w==

`protect key_keyowner="Mentor Graphics Corporation", key_keyname="MGC-VELOCE-RSA", key_method="rsa"
`protect encoding = (enctype="BASE64", line_length=76, bytes=128)
`protect key_block
ngggZ4AaOolK7F7zeqf8LCxDCGfbvArfgDzbRvoxE+aIi2H2/ZgHbrcaf1Km1cW+38j2kTOpZ5BU
JUI2G5HZNfsoiLXjFbOMvQQqByNzlhCZjrS3N725Cznvy/nQpUy+kW4iA6DQZKnpdC2s18Suxi5p
XtgDcUzCh62ABICOpz8=

`protect key_keyowner="Mentor Graphics Corporation", key_keyname="MGC-VERIF-SIM-RSA-2", key_method="rsa"
`protect encoding = (enctype="BASE64", line_length=76, bytes=256)
`protect key_block
FzAmLTVxyHRqX0WAddlPopAH/5r3ExgkeVujmhMcJXHbjZ+OKAHOMXTsnwDh03EpZ2Dn+0UPeR9J
JML3A+MQGMuUUzy/4d/lj5rriSnTu0eRK0uK6Gl8vjL08vO3UKb6wGj/w9CP45OWOkbMNgZzJkAl
ulPX0OUqymWYOn3WVAtIlaQ0dmpONV8p6Ixe9p5wlEtvy+7JjUPwaVnKlLjKSAaYD07OqMK+IOEP
5oYs2BscpZ3YKlKVJkoU493L7szHHn2LhSUrMld33nLuWIO6WPdo2u2pTnWXl/J1BzNaK1VaLx4R
H7VhIvgYcSlzCrtbQuNHKFtDPGhXjeA41TS29g==

`protect key_keyowner="Real Intent", key_keyname="RI-RSA-KEY-1", key_method="rsa"
`protect encoding = (enctype="BASE64", line_length=76, bytes=256)
`protect key_block
Oad6Ezs+KRRjlYrAkExu4Kft2T1qNa0HGt8W7O1ByK1ecBs0TGWt/sS3pnt6d6jWuqvsWhrmcGsU
TD7Z+IY65xRZ4IJfgngZD8v540FOGMuFUS31UWxcC7CI6qOo20Q0Irtoxrqm01u5p3tI87ApsE8S
lc2lQ5dh54cGYlRfmo5mYTw6WSHyyVYmoh9npUliD4eNVIKUqnBo1kmYzicnKe8ewFKTEWpjdMeZ
/4YxF/NRZzHTA3GIsnjcgOHia68T/NJJ+zQmoNwxerZWWoacU1EU0IHxET3y4fS/u0Af8OJhkGQf
jI0jGobNLRYYufemCxL6333z0oAno0RiPZlavA==

`protect key_keyowner="Xilinx", key_keyname="xilinxt_2023_11", key_method="rsa"
`protect encoding = (enctype="BASE64", line_length=76, bytes=256)
`protect key_block
LVIUY1x0cEHel3aUfppGw9v6zvpZmh/zrCgsFGWLi8t0vWUC/ikETYOpuFw/0f9L2t8c6tQj/BSQ
wjvzq42gFgtW+CFBjgHAVUBDHhzlv/GKUM/2Vq36bMg9H5f44nJH+7mDDGVPf2PyYZRkAosFPUpA
wRqTC/g2mQ0mMY/gZGQRrs+/VY69Ze9sjoEiEXuwkb/+/VjXgHCxiCzG4cKf0ZiQ+rePhqJqB7FK
IJ+6LHriZD474qtFLq3fOZ9mrqOgN7iBQlc66dO9E0RmZZZsWtQQzZ4q1c2pzvsjDdJyWe0mTlwa
QGVmYElSvL9in5WwDxoKM+2J7vco8OIexLgbJg==

`protect key_keyowner="Metrics Technologies Inc.", key_keyname="DSim", key_method="rsa"
`protect encoding = (enctype="BASE64", line_length=76, bytes=256)
`protect key_block
Qf9CPkJTDS6nRjzJ66HoyvpTqtDB4QY3Hy9peOp3xA39ggAvytqhHhiPv35dCRWSCdAyO1u2m+O7
/knms947I+MYTpHHfukyZsBbLho0jRq3cSXe9e6VE+4Dt40wryd91cmi93qmeUxg+vf0F91ug50P
gJ4oGYP71ANEq1UaGqGHgVK0ZsY6jTyc0x25eh+fnXg6vElSbqcptvyGMOBVT/g+gDKIheN40WzZ
Tday7b7o8j+UecVazn9OG8lGmgEQH+ilZfelpEFOBKoEc7YS6kKJ1yiX5nxRMJalTuojq5mhxebk
EsmPJe45gdIAuAmBpw3iLddcx52Arew1xpNY9w==

`protect key_keyowner="Atrenta", key_keyname="ATR-SG-RSA-1", key_method="rsa"
`protect encoding = (enctype="BASE64", line_length=76, bytes=384)
`protect key_block
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

`protect key_keyowner="Cadence Design Systems.", key_keyname="CDS_RSA_KEY_VER_1", key_method="rsa"
`protect encoding = (enctype="BASE64", line_length=76, bytes=256)
`protect key_block
WXM4aFffz6byfeUnRWfxJR3Sbg31hpZIfhJu9O4aqVdZMRQzhrArOJ75qYkGOgZjI+35a4DA9Ohc
RMh3Tm8A5kh9XM67B45s3+7vF8pYIM5pFlzEQBSQ/OeeAi6GNLI2ACXQl1WutRpQKuwX9iboEsRb
Kc1SU6AOV6yaliF6tUt1LL4x+bC8mqlEHTk6SvN7aiA23tVDcik1QSH66CO3/+J5f88G53DHDqtY
T6w2k7pUziwTnLfirI+XpPgqYp9YYRQEv52Q7wTYJlYnVYrMyludNuTaIE27AkgPAneEkdJlrq9l
eVOgs6ZIO1DEusKG7VzkbM1sS0GnU5Zhuj1Eww==

`protect key_keyowner="Synplicity", key_keyname="SYNP15_1", key_method="rsa"
`protect encoding = (enctype="BASE64", line_length=76, bytes=256)
`protect key_block
KJ2iLB3UgRnxezAEg3KJ/gREzXcLo8pOtacMRsDMsFCSD3vYAdGUKSARO8g71pIGFzJo6PBwogFR
MkJED/0TqwZaleoFaN2ULuSnzZGmf8vT0qKvutBGquDn8MH7T3k3wLxcNdZQLnkqisJCMj8u+71g
xMQRAkhtAQvA2cWb6TDQN6jmfByZuu/AH3X+YZ43XIDG/jymNkwyBWNNx0yzbZouJtOuzzYHhYoC
AAuKR+zfynO91P9hcrXFiExHtCmvb73DA4ICLGiOzEj+C1PMPBX9AHdhnWYy5BbQGsd727Y50yNo
xmTU1vBKL2ewwN4j/Ib2AK/Z7T+d/NunpRbCnA==

`protect key_keyowner="Mentor Graphics Corporation", key_keyname="MGC-PREC-RSA", key_method="rsa"
`protect encoding = (enctype="BASE64", line_length=76, bytes=256)
`protect key_block
eYDP9MWXRUmO05etuHvoqbEMRNQHmR5nos71kLkRxpycXrdpHxalQmyEdCdbeVoM8lN9qwxKuN0l
yQn00dSYRi3P02ygaVsHqVAsRtz2yRpIRjyGMYD7zKpnNQw476DBmK+/sCD7EH6NxSfzUNnfoURL
uIFC0sHEYpwX6Qt2bT2GdCC0OFvaGwQNimyTFdfeey7cdpg9JmsQRgLEUfRwG1Dk0iu258zTUnT+
31O5RA9OwlgZJpC+LpCvL8XAmGZJ4CCeUf2hnpppoV4KphAV4mCBUkNtUYZSJdF0a5cdHFxnxR5n
nI0ed4USMMiNvLqvP0HQgecfCvYzYx9kk0bmtA==

`protect data_method = "AES128-CBC"
`protect encoding = (enctype = "BASE64", line_length = 76, bytes = 79232)
`protect data_block
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
CIM=
`protect end_protected
library IEEE;
use IEEE.STD_LOGIC_1164.ALL;
library UNISIM;
use UNISIM.VCOMPONENTS.ALL;
entity bd_tb_uart_fifo_generator_0_0 is
  port (
    clk : in STD_LOGIC;
    rst : in STD_LOGIC;
    din : in STD_LOGIC_VECTOR ( 7 downto 0 );
    wr_en : in STD_LOGIC;
    rd_en : in STD_LOGIC;
    dout : out STD_LOGIC_VECTOR ( 7 downto 0 );
    full : out STD_LOGIC;
    empty : out STD_LOGIC
  );
  attribute NotValidForBitStream : boolean;
  attribute NotValidForBitStream of bd_tb_uart_fifo_generator_0_0 : entity is true;
  attribute CHECK_LICENSE_TYPE : string;
  attribute CHECK_LICENSE_TYPE of bd_tb_uart_fifo_generator_0_0 : entity is "USB_Serial_Test_fifo_generator_1_0,fifo_generator_v13_2_10,{}";
  attribute downgradeipidentifiedwarnings : string;
  attribute downgradeipidentifiedwarnings of bd_tb_uart_fifo_generator_0_0 : entity is "yes";
  attribute x_core_info : string;
  attribute x_core_info of bd_tb_uart_fifo_generator_0_0 : entity is "fifo_generator_v13_2_10,Vivado 2024.1";
end bd_tb_uart_fifo_generator_0_0;
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
